Swonkie/DeskFighter/PCB/DeskFighter/3dmodels/Encoder_Cap.step

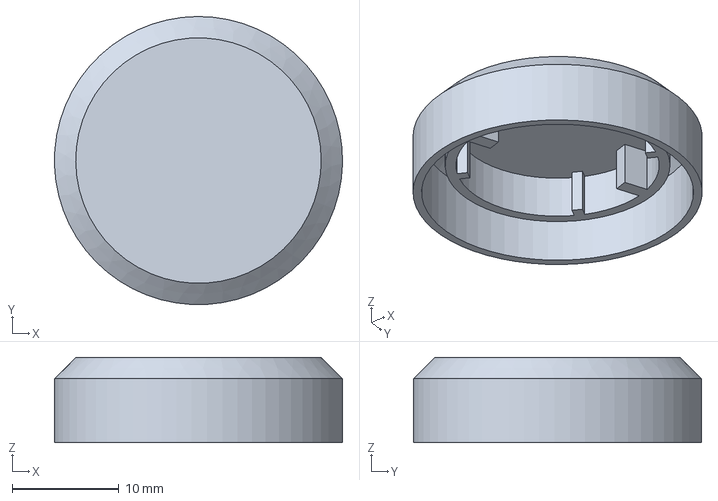
[picture p15: CAD file, 2026-08-21]
PCB/DeskFighter/3dmodels/Encoder_Cap.step
27.0 x 27.0 x 8.00 mm
