Swonkie/DeskFighter/PCB/MacroPad/3dmodels/Stabilizer_2.00u.step

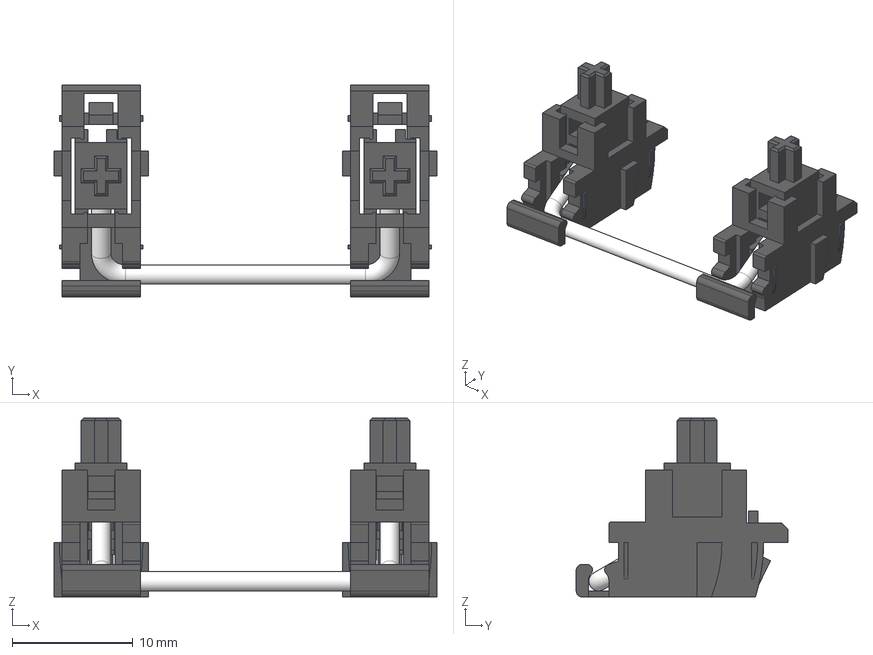
[picture p16: CAD file, 2026-08-21]
PCB/MacroPad/3dmodels/Stabilizer_2.00u.step
31.7 x 17.5 x 14.8 mm
stem_l
body_l
stem_r
body_r
wire_2u
