Swonkie/DeskFighter/3D Printed Parts/Keycaps.3mf

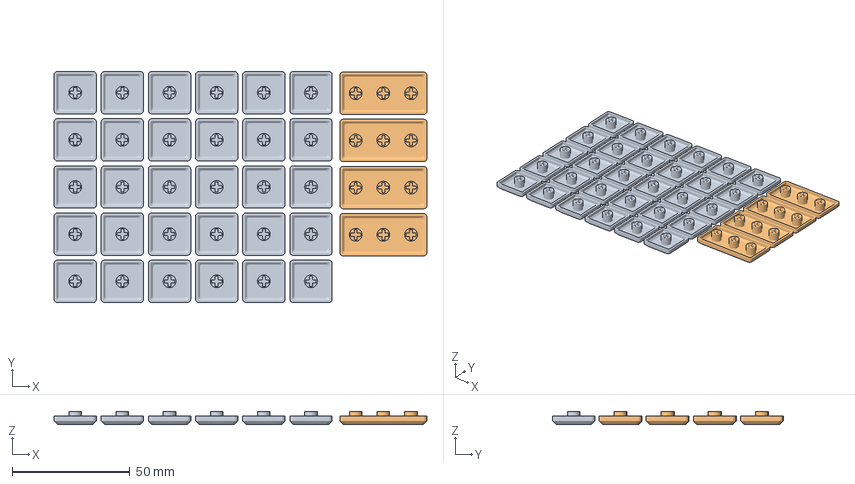
[picture p17: CAD file, 2026-08-21]
3D Printed Parts/Keycaps.3mf
158.2 x 98.0 x 5.50 mm
Keycaps_1u
Keycaps_2u
